makinteractlab/VirtualWire/Software/VirtualWire_User_App/VW_Eagle/data/img/BT.png

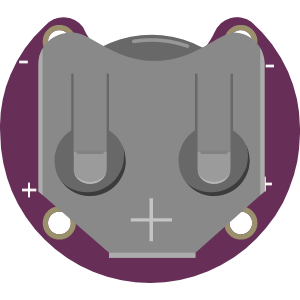
Software/VirtualWire_User_App/VW_Eagle/data/img/BT.png
