makinteractlab/VirtualWire/Software/VirtualWire_User_App/VW_Eagle/data/img/C.png

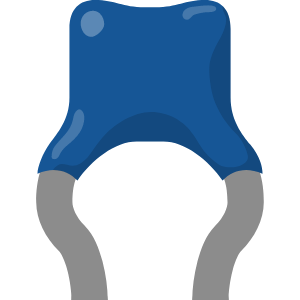
Software/VirtualWire_User_App/VW_Eagle/data/img/C.png
