makinteractlab/VirtualWire/Software/VirtualWire_User_App/VW_Eagle/data/img/CP.png

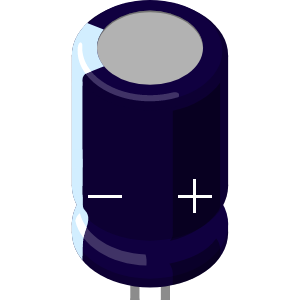
Software/VirtualWire_User_App/VW_Eagle/data/img/CP.png
