makinteractlab/VirtualWire/Software/VirtualWire_User_App/VW_Eagle/data/img/DE.png

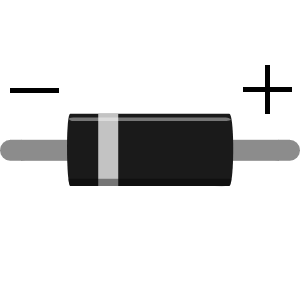
Software/VirtualWire_User_App/VW_Eagle/data/img/DE.png
