makinteractlab/VirtualWire/Software/VirtualWire_User_App/VW_Eagle/data/img/LED.png

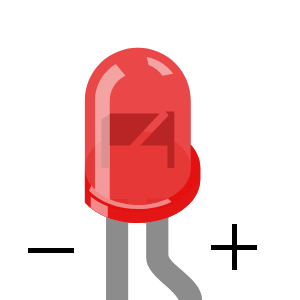
Software/VirtualWire_User_App/VW_Eagle/data/img/LED.png
