makinteractlab/VirtualWire/Software/VirtualWire_User_App/VW_Eagle/data/img/PB.png

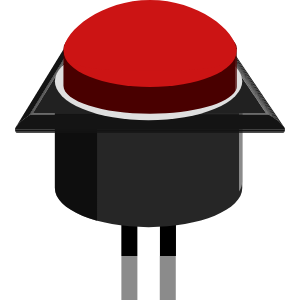
Software/VirtualWire_User_App/VW_Eagle/data/img/PB.png
