makinteractlab/VirtualWire/Software/VirtualWire_User_App/VW_Eagle/data/img/R.png

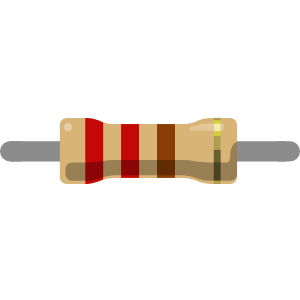
Software/VirtualWire_User_App/VW_Eagle/data/img/R.png
