makinteractlab/VirtualWire/Software/VirtualWire_User_App/VW_Eagle/data/img/RP.png

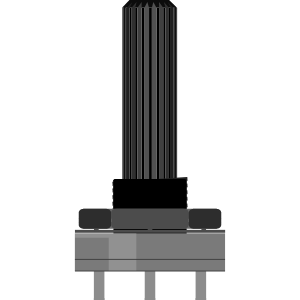
Software/VirtualWire_User_App/VW_Eagle/data/img/RP.png
