makinteractlab/VirtualWire/Software/VirtualWire_User_App/VW_Eagle/data/img/SV.png

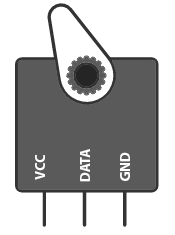
Software/VirtualWire_User_App/VW_Eagle/data/img/SV.png
