makinteractlab/VirtualWire/Software/VirtualWire_User_App/VW_Eagle/data/img/UC.png

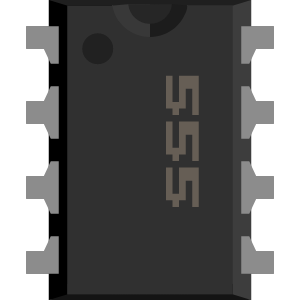
Software/VirtualWire_User_App/VW_Eagle/data/img/UC.png
