makinteractlab/VirtualWire/Software/VirtualWireStandalone/data/ArduinoUno.png

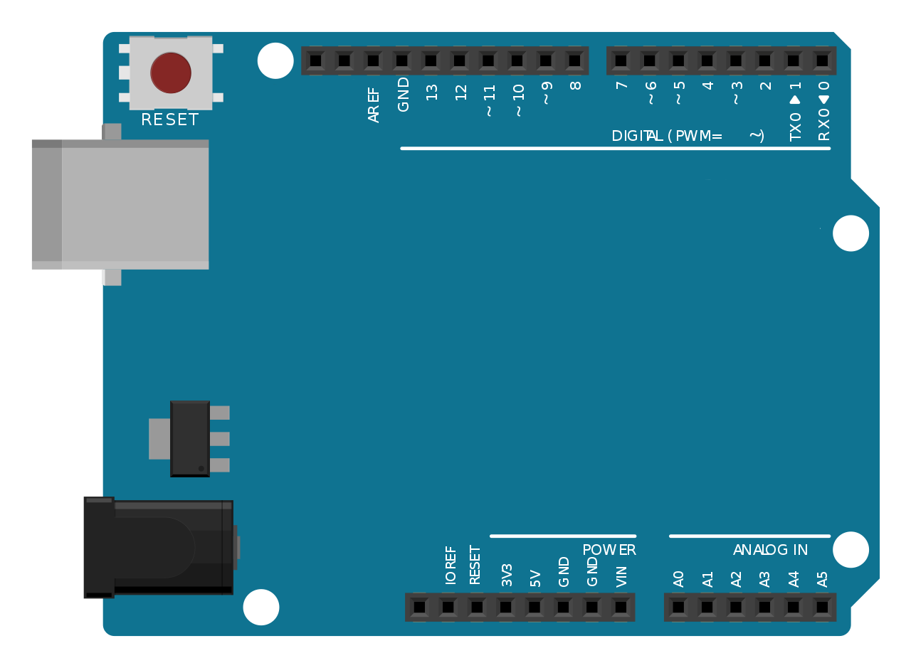
Software/VirtualWireStandalone/data/ArduinoUno.png
