makinteractlab/VirtualWire/Software/VirtualWire_User_App/VW_Eagle/data/Eagle/VW.sch

## EAGLE design Software/VirtualWire_User_App/VW_Eagle/data/Eagle/VW.sch (2019-09-11)

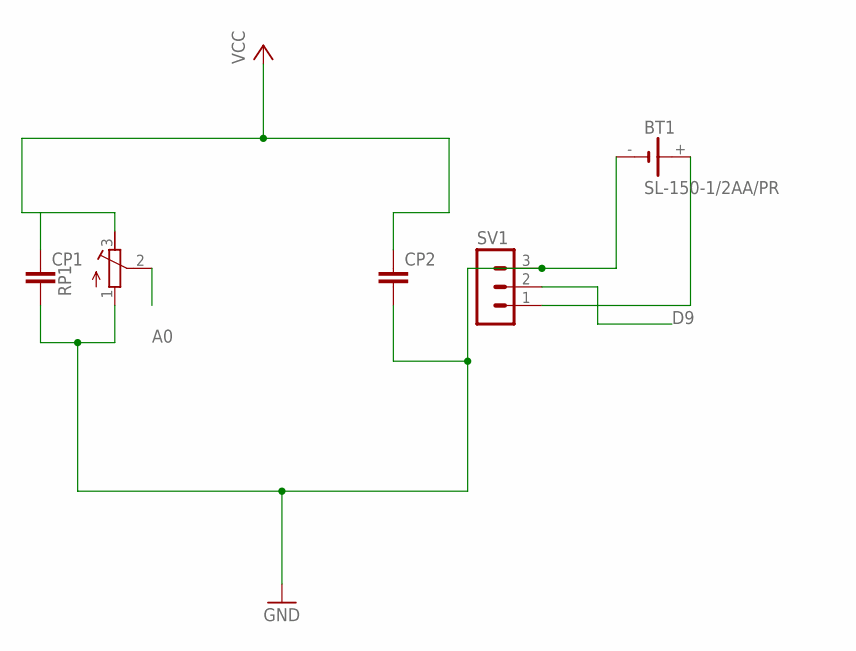
[picture p21: schematic VW.sch]

Parts:
BT1: SL-150-1/2AA/PR
CP1, CP2: C2,5-3; C2.5-3
RP1: R-TRIMM4G/J; RTRIM4G/J
SV1: MA03-1

Connections:
A0: RP1.2 (S)
A5V: CP1.1, CP2.1, RP1.3 (E)
D9: SV1.2
GND1: BT1.-, CP1.2, CP2.2, RP1.1 (A), SV1.3
unnamed: BT1.+, SV1.1
