makinteractlab/VirtualWire/Software/VirtualWire_User_App/merge_test/data/Eagle/VW.sch

## EAGLE design Software/VirtualWire_User_App/merge_test/data/Eagle/VW.sch (2019-09-11)

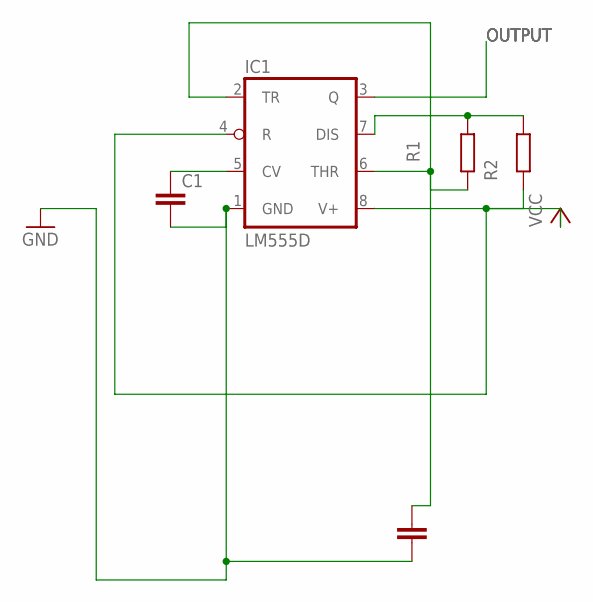
[picture p22: schematic VW.sch]

Parts:
C1, C3: C-EU025-024X044; C025-024X044
IC1: LM555D; SO08
R1, R2: R-EU_0204/5; 0204/5

Connections:
GND: C1.2, C3.2, IC1.1 (GND)
unnamed: IC1.7 (DIS), R1.2, R2.1
unnamed: C3.1, IC1.2 (TR), IC1.6 (THR), R1.1
unnamed: C1.1, IC1.5 (CV)
OUTPUT: IC1.3 (Q)
VCC: IC1.4 (R), IC1.8 (V+), R2.2
