makinteractlab/VirtualWire/Software/VirtualWire_User_App/Sample_Schematic_File/555_Timer.sch

## EAGLE design Software/VirtualWire_User_App/Sample_Schematic_File/555_Timer.sch (2019-09-11)

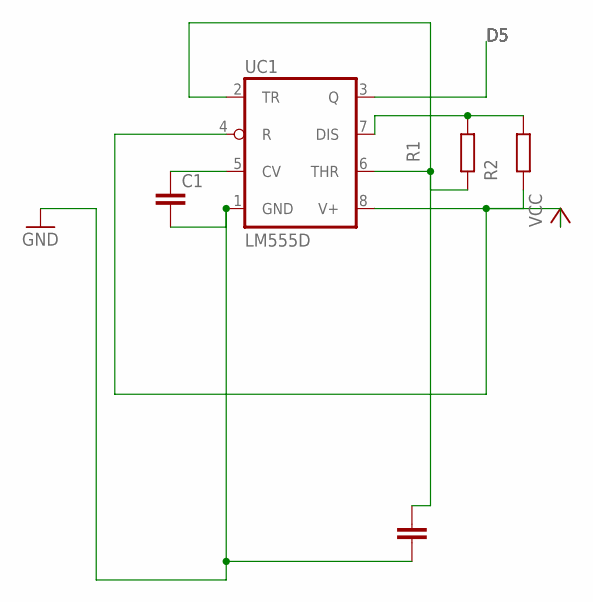
[picture p23: schematic 555_Timer.sch]

Parts:
C1, C3: C-EU025-024X044; C025-024X044
R1, R2: R-EU_0204/5; 0204/5
UC1: LM555D; SO08

Connections:
D5: UC1.3 (Q)
GND: C1.2, C3.2, UC1.1 (GND)
unnamed: R1.2, R2.1, UC1.7 (DIS)
unnamed: C3.1, R1.1, UC1.2 (TR), UC1.6 (THR)
unnamed: C1.1, UC1.5 (CV)
VCC: R2.2, UC1.4 (R), UC1.8 (V+)
