makinteractlab/VirtualWire/Software/VirtualWire_User_App/Sample_Schematic_File/VW.sch

## EAGLE design Software/VirtualWire_User_App/Sample_Schematic_File/VW.sch (2019-09-11)

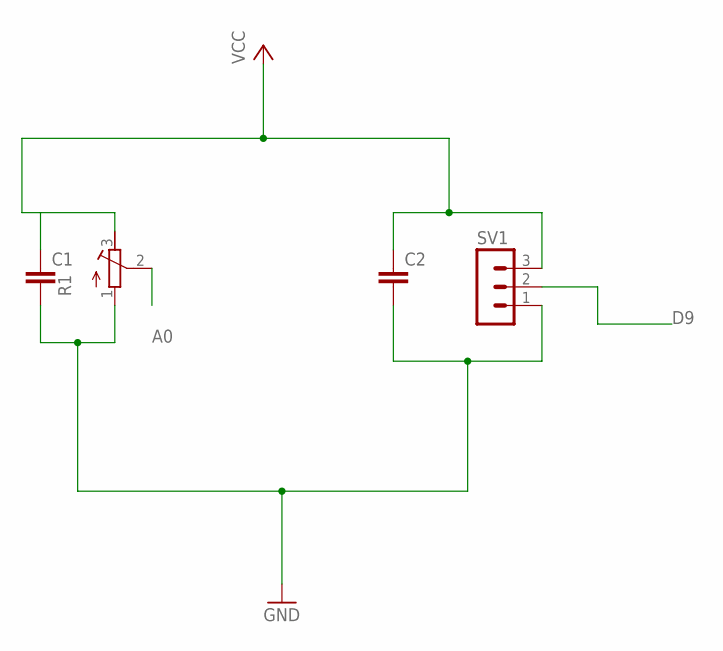
[picture p24: schematic VW.sch]

Parts:
C1, C2: C2,5-3; C2.5-3
R1: R-TRIMM4G/J; RTRIM4G/J
SV1: MA03-1

Connections:
A0: R1.2 (S)
A5V: C1.1, C2.1, R1.3 (E), SV1.3
D9: SV1.2
GND1: C1.2, C2.2, R1.1 (A), SV1.1
