makinteractlab/VirtualWire/Software/VirtualWireStandalone/Coordinate_Handler.pde

void cood_tester(){
  fill(255, 0, 0);
  ellipse(nodeToPixel("SCL").x, nodeToPixel("SCL").y, 10, 10);
  ellipse(nodeToPixel("SDA").x, nodeToPixel("SDA").y, 10, 10);
  ellipse(nodeToPixel("AREF").x, nodeToPixel("AREF").y, 10, 10);
  ellipse(nodeToPixel("GND1").x, nodeToPixel("GND1").y, 10, 10);
  ellipse(nodeToPixel("D13").x, nodeToPixel("D13").y, 10, 10);
  ellipse(nodeToPixel("D12").x, nodeToPixel("D12").y, 10, 10);
  ellipse(nodeToPixel("D11").x, nodeToPixel("D11").y, 10, 10);
  ellipse(nodeToPixel("D10").x, nodeToPixel("D10").y, 10, 10);
  ellipse(nodeToPixel("D9").x, nodeToPixel("D9").y, 10, 10);
  ellipse(nodeToPixel("D8").x, nodeToPixel("D8").y, 10, 10);
  ellipse(nodeToPixel("D7").x, nodeToPixel("D7").y, 10, 10);
  ellipse(nodeToPixel("D6").x, nodeToPixel("D6").y, 10, 10);
  ellipse(nodeToPixel("D5").x, nodeToPixel("D5").y, 10, 10);
  ellipse(nodeToPixel("D4").x, nodeToPixel("D4").y, 10, 10);
  ellipse(nodeToPixel("D3").x, nodeToPixel("D3").y, 10, 10);
  ellipse(nodeToPixel("D2").x, nodeToPixel("D2").y, 10, 10);
  ellipse(nodeToPixel("D1").x, nodeToPixel("D1").y, 10, 10);
  ellipse(nodeToPixel("D0").x, nodeToPixel("D0").y, 10, 10);
  
  ellipse(nodeToPixel("N/C").x, nodeToPixel("N/C").y, 10, 10);
  ellipse(nodeToPixel("IOREF").x, nodeToPixel("IOREF").y, 10, 10);
  ellipse(nodeToPixel("RESET").x, nodeToPixel("RESET").y, 10, 10);
  ellipse(nodeToPixel("A3V").x, nodeToPixel("A3V").y, 10, 10);
  ellipse(nodeToPixel("A5V").x, nodeToPixel("A5V").y, 10, 10);
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
  ellipse(nodeToPixel("ROW12-2").x, nodeToPixel("ROW12-2").y, 10, 10);
  ellipse(nodeToPixel("ROW13-2").x, nodeToPixel("ROW13-2").y, 10, 10);
  ellipse(nodeToPixel("ROW14-2").x, nodeToPixel("ROW14-2").y, 10, 10);
  ellipse(nodeToPixel("ROW15-2").x, nodeToPixel("ROW15-2").y, 10, 10);
  ellipse(nodeToPixel("ROW16-2").x, nodeToPixel("ROW16-2").y, 10, 10);
  
  ellipse(nodeToPixel("ROW9-3").x, nodeToPixel("ROW9-3").y, 10, 10);
  ellipse(nodeToPixel("ROW10-3").x, nodeToPixel("ROW10-3").y, 10, 10);
  ellipse(nodeToPixel("ROW11-3").x, nodeToPixel("ROW11-3").y, 10, 10);
  ellipse(nodeToPixel("ROW12-3").x, nodeToPixel("ROW12-3").y, 10, 10);
  ellipse(nodeToPixel("ROW13-3").x, nodeToPixel("ROW13-3").y, 10, 10);
  ellipse(nodeToPixel("ROW14-3").x, nodeToPixel("ROW14-3").y, 10, 10);
  ellipse(nodeToPixel("ROW15-3").x, nodeToPixel("ROW15-3").y, 10, 10);
  ellipse(nodeToPixel("ROW16-3").x, nodeToPixel("ROW16-3").y, 10, 10);
  
  ellipse(nodeToPixel("ROW9-4").x, nodeToPixel("ROW9-4").y, 10, 10);
  ellipse(nodeToPixel("ROW10-4").x, nodeToPixel("ROW10-4").y, 10, 10);
  ellipse(nodeToPixel("ROW11-4").x, nodeToPixel("ROW11-4").y, 10, 10);
  ellipse(nodeToPixel("ROW12-4").x, nodeToPixel("ROW12-4").y, 10, 10);
  ellipse(nodeToPixel("ROW13-4").x, nodeToPixel("ROW13-4").y, 10, 10);
  ellipse(nodeToPixel("ROW14-4").x, nodeToPixel("ROW14-4").y, 10, 10);
  ellipse(nodeToPixel("ROW15-4").x, nodeToPixel("ROW15-4").y, 10, 10);
  ellipse(nodeToPixel("ROW16-4").x, nodeToPixel("ROW16-4").y, 10, 10);
  
  ellipse(nodeToPixel("ROW9-5").x, nodeToPixel("ROW9-5").y, 10, 10);
  ellipse(nodeToPixel("ROW10-5").x, nodeToPixel("ROW10-5").y, 10, 10);
  ellipse(nodeToPixel("ROW11-5").x, nodeToPixel("ROW11-5").y, 10, 10);
  ellipse(nodeToPixel("ROW12-5").x, nodeToPixel("ROW12-5").y, 10, 10);
  ellipse(nodeToPixel("ROW13-5").x, nodeToPixel("ROW13-5").y, 10, 10);
  ellipse(nodeToPixel("ROW14-5").x, nodeToPixel("ROW14-5").y, 10, 10);
  ellipse(nodeToPixel("ROW15-5").x, nodeToPixel("ROW15-5").y, 10, 10);
  ellipse(nodeToPixel("ROW16-5").x, nodeToPixel("ROW16-5").y, 10, 10);
}

PVector nodeToPixel(String node){
  int h1 = 108;
  int w1 = 355;
  int w2 = 647;
  float s1 = 27;
  
  if(node.equals("SCL")) return new PVector(w1, h1);
  if(node.equals("SDA")) return new PVector(w1 + s1, h1);
  if(node.equals("AREF")) return new PVector(w1 + 2*s1, h1);
  if(node.equals("GND1")) return new PVector(w1 + 3*s1, h1);
  if(node.equals("D13")) return new PVector(w1 + 4*s1, h1);
  if(node.equals("D12")) return new PVector(w1 + 5*s1, h1);
  if(node.equals("D11")) return new PVector(w1 + 6*s1, h1);
  if(node.equals("D10")) return new PVector(w1 + 7*s1 + 1, h1);
  if(node.equals("D9")) return new PVector(w1 + 8*s1 + 2, h1);
  if(node.equals("D8")) return new PVector(w1 + 9*s1 + 3, h1);
  
  if(node.equals("D7")) return new PVector(w2, h1);
  if(node.equals("D6")) return new PVector(w2 + s1, h1);
  if(node.equals("D5")) return new PVector(w2 + 2*s1, h1);
  if(node.equals("D4")) return new PVector(w2 + 3*s1, h1);
  if(node.equals("D3")) return new PVector(w2 + 4*s1, h1);
  if(node.equals("D2")) return new PVector(w2 + 5*s1 + 1, h1);
  if(node.equals("D1")) return new PVector(w2 + 6*s1 + 2, h1);
  if(node.equals("D0")) return new PVector(w2 + 7*s1 + 2, h1);
  
  int h2 = 640;
  int w3 = 453;
  int w4 = 702;
  
  if(node.equals("N/C")) return new PVector(w3, h2);
  if(node.equals("IOREF")) return new PVector(w3 + s1, h2);
  if(node.equals("RESET")) return new PVector(w3 + 2*s1, h2);
  if(node.equals("A3V")) return new PVector(w3 + 3*s1, h2);
  if(node.equals("A5V")) return new PVector(w3 + 4*s1 + 2, h2);
  if(node.equals("GND2")) return new PVector(w3 + 5*s1 + 2, h2);
  if(node.equals("GND3")) return new PVector(w3 + 6*s1 + 3, h2);
  if(node.equals("VIN")) return new PVector(w3 + 7*s1 + 3, h2);
  
  if(node.equals("A0")) return new PVector(w4, h2);
  if(node.equals("A1")) return new PVector(w4 + s1, h2);
  if(node.equals("A2")) return new PVector(w4 + 2*s1, h2);
  if(node.equals("A3")) return new PVector(w4 + 3*s1, h2);
  if(node.equals("A4")) return new PVector(w4 + 4*s1 + 2, h2);
  if(node.equals("A5")) return new PVector(w4 + 5*s1 + 2, h2);
  
  int h3 = 230;
  int w5_1 = 332;
  int w5_2 = 332 + 44;
  int w5_3 = 332 + 44*2;
  int w5_4 = 332 + 44*3;
  int w5_5 = 332 + 44*4;
  int w6_1 = 620;
  int w6_2 = 620 + 44;
  int w6_3 = 620 + 44*2;
  int w6_4 = 620 + 44*3;
  int w6_5 = 620 + 44*4;
  int s2 = 44;
  
  if(node.equals("ROW1-1")) return new PVector(w5_1, h3);
  if(node.equals("ROW2-1")) return new PVector(w5_1, h3 + s2);
  if(node.equals("ROW3-1")) return new PVector(w5_1, h3 + 2*s2);
  if(node.equals("ROW4-1")) return new PVector(w5_1, h3 + 3*s2);
  if(node.equals("ROW5-1")) return new PVector(w5_1, h3 + 4*s2 - 1);
  if(node.equals("ROW6-1")) return new PVector(w5_1, h3 + 5*s2 - 1);
  if(node.equals("ROW7-1")) return new PVector(w5_1, h3 + 6*s2 - 2);
  if(node.equals("ROW8-1")) return new PVector(w5_1, h3 + 7*s2 - 2);
  
  if(node.equals("ROW1-2")) return new PVector(w5_2, h3);
  if(node.equals("ROW2-2")) return new PVector(w5_2, h3 + s2);
  if(node.equals("ROW3-2")) return new PVector(w5_2, h3 + 2*s2);
  if(node.equals("ROW4-2")) return new PVector(w5_2, h3 + 3*s2);
  if(node.equals("ROW5-2")) return new PVector(w5_2, h3 + 4*s2 - 1);
  if(node.equals("ROW6-2")) return new PVector(w5_2, h3 + 5*s2 - 1);
  if(node.equals("ROW7-2")) return new PVector(w5_2, h3 + 6*s2 - 2);
  if(node.equals("ROW8-2")) return new PVector(w5_2, h3 + 7*s2 - 2);
  
  if(node.equals("ROW1-3")) return new PVector(w5_3, h3);
  if(node.equals("ROW2-3")) return new PVector(w5_3, h3 + s2);
  if(node.equals("ROW3-3")) return new PVector(w5_3, h3 + 2*s2);
  if(node.equals("ROW4-3")) return new PVector(w5_3, h3 + 3*s2);
  if(node.equals("ROW5-3")) return new PVector(w5_3, h3 + 4*s2 - 1);
  if(node.equals("ROW6-3")) return new PVector(w5_3, h3 + 5*s2 - 1);
  if(node.equals("ROW7-3")) return new PVector(w5_3, h3 + 6*s2 - 2);
  if(node.equals("ROW8-3")) return new PVector(w5_3, h3 + 7*s2 - 2);
  
  if(node.equals("ROW1-4")) return new PVector(w5_4, h3);
  if(node.equals("ROW2-4")) return new PVector(w5_4, h3 + s2);
  if(node.equals("ROW3-4")) return new PVector(w5_4, h3 + 2*s2);
  if(node.equals("ROW4-4")) return new PVector(w5_4, h3 + 3*s2);
  if(node.equals("ROW5-4")) return new PVector(w5_4, h3 + 4*s2 - 1);
  if(node.equals("ROW6-4")) return new PVector(w5_4, h3 + 5*s2 - 1);
  if(node.equals("ROW7-4")) return new PVector(w5_4, h3 + 6*s2 - 2);
  if(node.equals("ROW8-4")) return new PVector(w5_4, h3 + 7*s2 - 2);
  
  if(node.equals("ROW1-5")) return new PVector(w5_5, h3);
  if(node.equals("ROW2-5")) return new PVector(w5_5, h3 + s2);
  if(node.equals("ROW3-5")) return new PVector(w5_5, h3 + 2*s2);
  if(node.equals("ROW4-5")) return new PVector(w5_5, h3 + 3*s2);
  if(node.equals("ROW5-5")) return new PVector(w5_5, h3 + 4*s2 - 1);
  if(node.equals("ROW6-5")) return new PVector(w5_5, h3 + 5*s2 - 1);
  if(node.equals("ROW7-5")) return new PVector(w5_5, h3 + 6*s2 - 2);
  if(node.equals("ROW8-5")) return new PVector(w5_5, h3 + 7*s2 - 2);
  
  if(node.equals("ROW9-1")) return new PVector(w6_1, h3);
  if(node.equals("ROW10-1")) return new PVector(w6_1, h3 + s2);
  if(node.equals("ROW11-1")) return new PVector(w6_1, h3 + 2*s2);
  if(node.equals("ROW12-1")) return new PVector(w6_1, h3 + 3*s2);
  if(node.equals("ROW13-1")) return new PVector(w6_1, h3 + 4*s2 - 1);
  if(node.equals("ROW14-1")) return new PVector(w6_1, h3 + 5*s2 - 1);
  if(node.equals("ROW15-1")) return new PVector(w6_1, h3 + 6*s2 - 2);
  if(node.equals("ROW16-1")) return new PVector(w6_1, h3 + 7*s2 - 2);
  
  if(node.equals("ROW9-2")) return new PVector(w6_2, h3);
  if(node.equals("ROW10-2")) return new PVector(w6_2, h3 + s2);
  if(node.equals("ROW11-2")) return new PVector(w6_2, h3 + 2*s2);
  if(node.equals("ROW12-2")) return new PVector(w6_2, h3 + 3*s2);
  if(node.equals("ROW13-2")) return new PVector(w6_2, h3 + 4*s2 - 1);
  if(node.equals("ROW14-2")) return new PVector(w6_2, h3 + 5*s2 - 1);
  if(node.equals("ROW15-2")) return new PVector(w6_2, h3 + 6*s2 - 2);
  if(node.equals("ROW16-2")) return new PVector(w6_2, h3 + 7*s2 - 2);
  
  if(node.equals("ROW9-3")) return new PVector(w6_3, h3);
  if(node.equals("ROW10-3")) return new PVector(w6_3, h3 + s2);
  if(node.equals("ROW11-3")) return new PVector(w6_3, h3 + 2*s2);
  if(node.equals("ROW12-3")) return new PVector(w6_3, h3 + 3*s2);
  if(node.equals("ROW13-3")) return new PVector(w6_3, h3 + 4*s2 - 1);
  if(node.equals("ROW14-3")) return new PVector(w6_3, h3 + 5*s2 - 1);
  if(node.equals("ROW15-3")) return new PVector(w6_3, h3 + 6*s2 - 2);
  if(node.equals("ROW16-3")) return new PVector(w6_3, h3 + 7*s2 - 2);
  
  if(node.equals("ROW9-4")) return new PVector(w6_4, h3);
  if(node.equals("ROW10-4")) return new PVector(w6_4, h3 + s2);
  if(node.equals("ROW11-4")) return new PVector(w6_4, h3 + 2*s2);
  if(node.equals("ROW12-4")) return new PVector(w6_4, h3 + 3*s2);
  if(node.equals("ROW13-4")) return new PVector(w6_4, h3 + 4*s2 - 1);
  if(node.equals("ROW14-4")) return new PVector(w6_4, h3 + 5*s2 - 1);
  if(node.equals("ROW15-4")) return new PVector(w6_4, h3 + 6*s2 - 2);
  if(node.equals("ROW16-4")) return new PVector(w6_4, h3 + 7*s2 - 2);
  
  if(node.equals("ROW9-5")) return new PVector(w6_5, h3);
  if(node.equals("ROW10-5")) return new PVector(w6_5, h3 + s2);
  if(node.equals("ROW11-5")) return new PVector(w6_5, h3 + 2*s2);
  if(node.equals("ROW12-5")) return new PVector(w6_5, h3 + 3*s2);
  if(node.equals("ROW13-5")) return new PVector(w6_5, h3 + 4*s2 - 1);
  if(node.equals("ROW14-5")) return new PVector(w6_5, h3 + 5*s2 - 1);
  if(node.equals("ROW15-5")) return new PVector(w6_5, h3 + 6*s2 - 2);
  if(node.equals("ROW16-5")) return new PVector(w6_5, h3 + 7*s2 - 2);
  
  return new PVector(-7, -7);
}
