makinteractlab/VirtualWire/Software/VirtualWireStandalone/Event_Handler.pde

void mousePressed(){
  if(mouseFlag == false && mouseX < 940){
    //println("mouse down");
    mouseFlag = true;
    lineAnchorX = mouseX;
    lineAnchorY = mouseY;
  }
}

void mouseReleased(){
  //println("mouse up");
  mouseFlag = false;
  
  int currX = mouseX;
  int currY = mouseY;
  
  if(!checkWithinNode(lineAnchorX, lineAnchorY).equals("null") && !checkWithinNode(currX, currY).equals("null")){
    String from = checkWithinNode(lineAnchorX, lineAnchorY);
    String to = checkWithinNode(currX, currY);
    
    if(!from.equals(to)) wirelist.add(new Wire(from, to, lineAnchorX, lineAnchorY, currX, currY));
    
    lb.clear();
    
    for(int i = 0; i < wirelist.size(); i++) {
      lb.addItem(wirelist.get(i).getButtonLabel(), i);
    }
  }
}

void history(int x) {
  println("deleting " + wirelist.get(x).getButtonLabel());
  lb.clear();
  
  wirelist.remove(x);
  
  for(int i = 0; i < wirelist.size(); i++) {
    lb.addItem(wirelist.get(i).getButtonLabel(), i);
  }
}

void actionPerformed (GUIEvent e) {
  if (e.getSource() == b1) {
    for(int i = 0; i < wirelist.size(); i++){
      println("Wire #" + (i + 1));
      println(wirelist.get(i));
    }
    updateCommands_Multi();
    printAllCommands();
    runAllCommands();
  }
  
  if (e.getSource() == b2) {
    println();
    println("WIRES CLEARED");
    
    wirelist.clear();
    lb.clear();
    
    println("SENDING RESET COMMAND");
  
    String runThis = "{\"cmd\":\"reset\"}" + "\n";
    println("{\"cmd\":\"reset\"}" + " - sent to VW Board");
    myPort.write(runThis);
  }
  
  //if(e.getSource() == b3) {
  //  println("SENDING RESET COMMAND");
  //
  //  String runThis = "{\"cmd\":\"reset\"}" + "\n";
  //  println("{\"cmd\":\"reset\"}" + " - sent to VW Board");
  //  myPort.write(runThis);
  //}
}


void serialEvent(Serial p) {
  inString = p.readStringUntil(10);
  if(inString != null){
    println(inString + " - received from VW Board");
    serialCmdIndex++;
    
    if(serialCmdIndex < commandList.size()){
      String runThis = commandList.get(serialCmdIndex) + "\n";
      println(commandList.get(serialCmdIndex));
      myPort.write(runThis);
    }else{
      serialCmdIndex = 0;
      println("BOARD CONNECTIONS UPDATED");
    }
  }
  
}
